jerome-labidurie/vatx/pictures/vatx_3D_v2.0.png

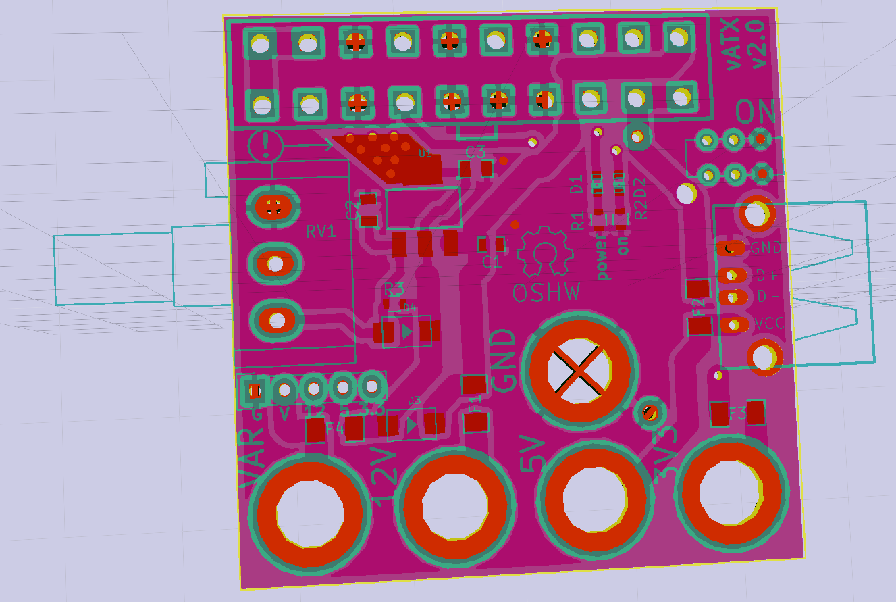
pictures/vatx_3D_v2.0.png
