jerome-labidurie/vatx/pictures/vatx_3D_v2.0_2.png

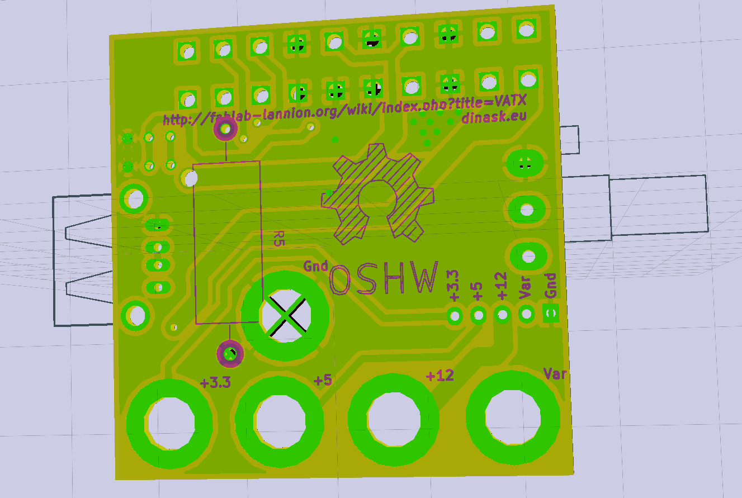
pictures/vatx_3D_v2.0_2.png
