jerome-labidurie/vatx/pictures/vatx_box_v2.2.png

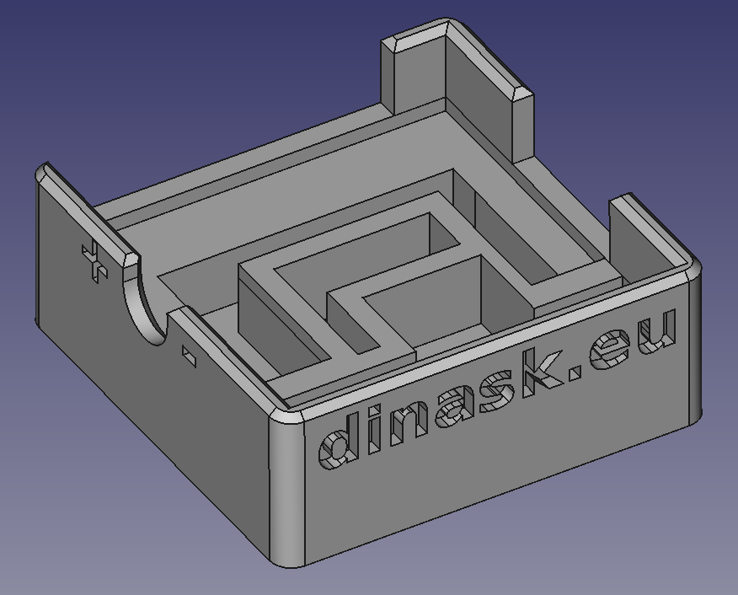
pictures/vatx_box_v2.2.png
