jerome-labidurie/vatx/pictures/vatx_proto_0_3.jpg

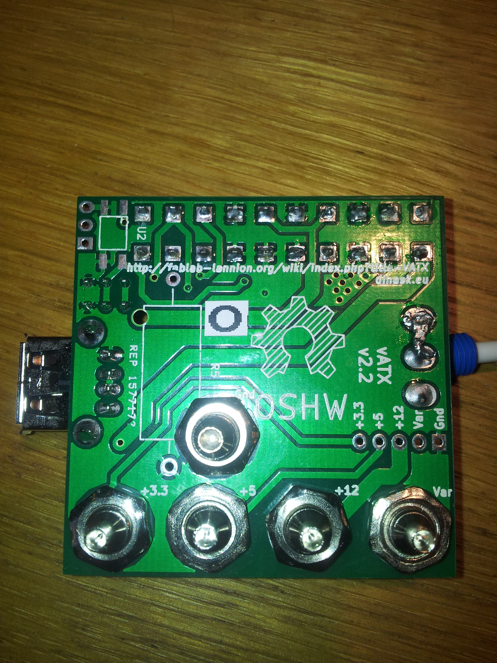
pictures/vatx_proto_0_3.jpg
